josefadamcik/stanakeyboard/doc/model_1.png

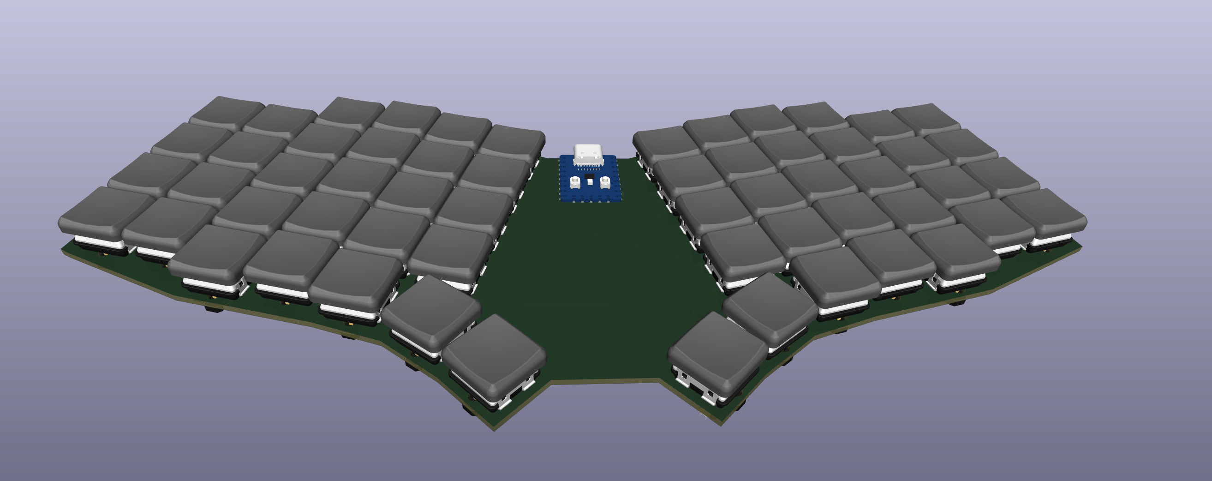
doc/model_1.png
