josefadamcik/stanakeyboard/case/MiddleCover2.3mf

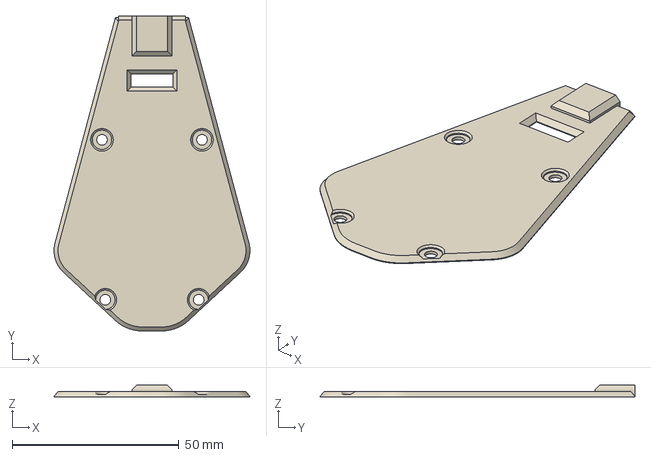
[picture p18: CAD file, 2023-04-15]
case/MiddleCover2.3mf
58.8 x 94.5 x 3.60 mm
